zmushko/Nostromo/case/pimpa.scad

d=6;
h=6;

base=10;
base_h=2;


translate(0, 0, 0) 
    cylinder(d=d,h=h, $fn=32);

translate(0, 0, 0)
    cylinder(d=base, h=base_h, $fn=32);
